oclyke-dev/RainbowForest/process_documentation/IMG_0713.JPG

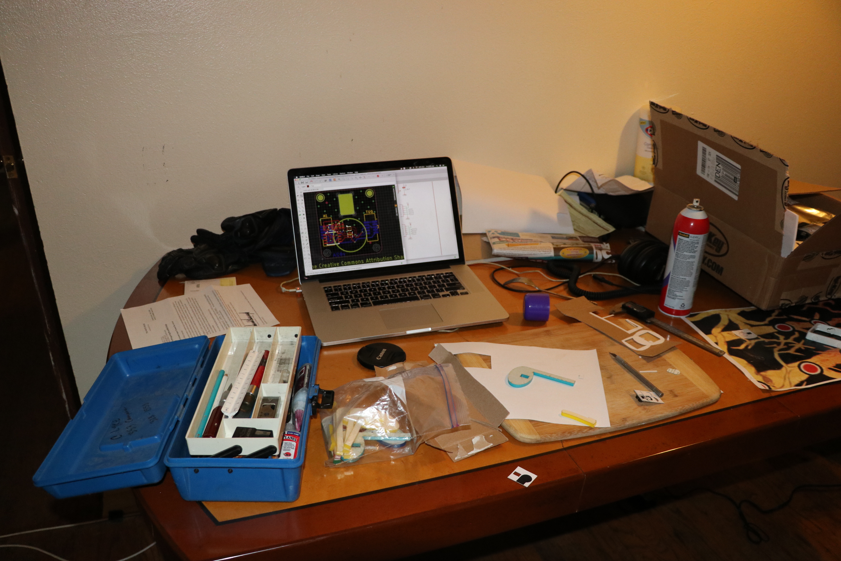
process_documentation/IMG_0713.JPG
