oclyke-dev/RainbowForest/process_documentation/IMG_0714.JPG

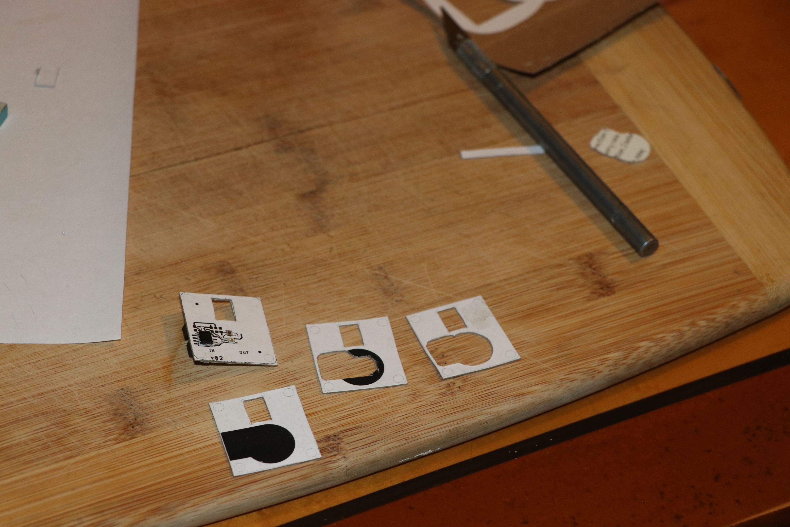
process_documentation/IMG_0714.JPG
