oclyke-dev/RainbowForest/process_documentation/IMG_0716.JPG

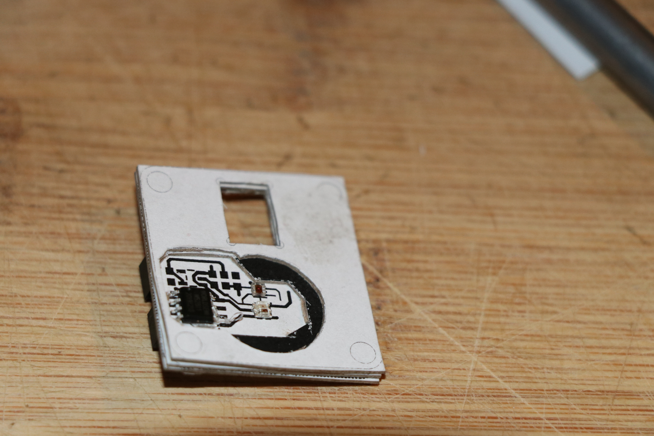
process_documentation/IMG_0716.JPG
