oclyke-dev/RainbowForest/process_documentation/IMG_0717.JPG

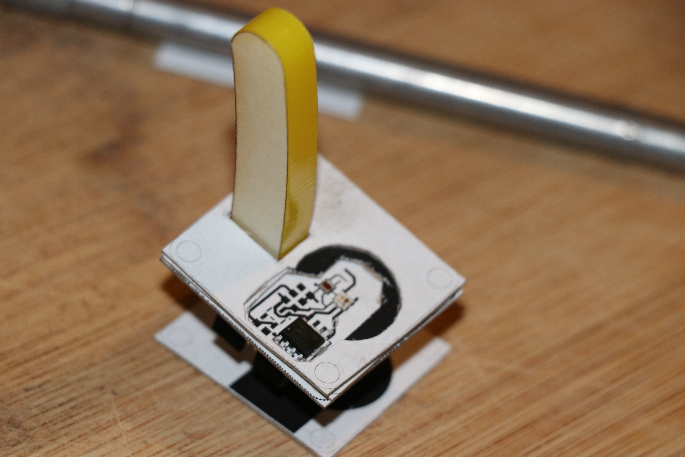
process_documentation/IMG_0717.JPG
