oclyke-dev/RainbowForest/process_documentation/IMG_0719.JPG

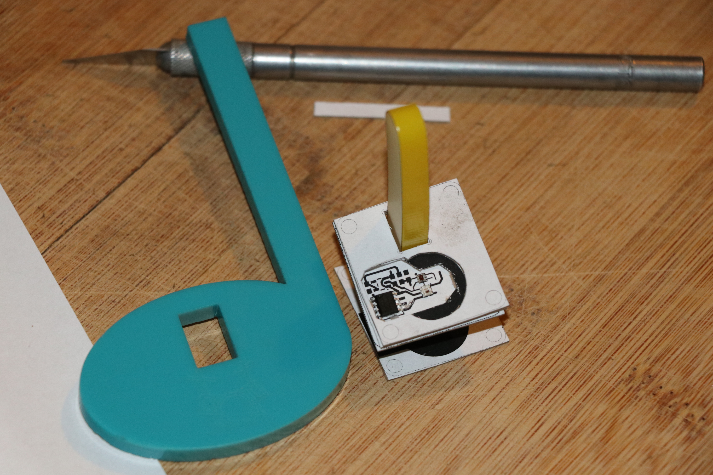
process_documentation/IMG_0719.JPG
