oclyke-dev/RainbowForest/process_documentation/IMG_0720.JPG

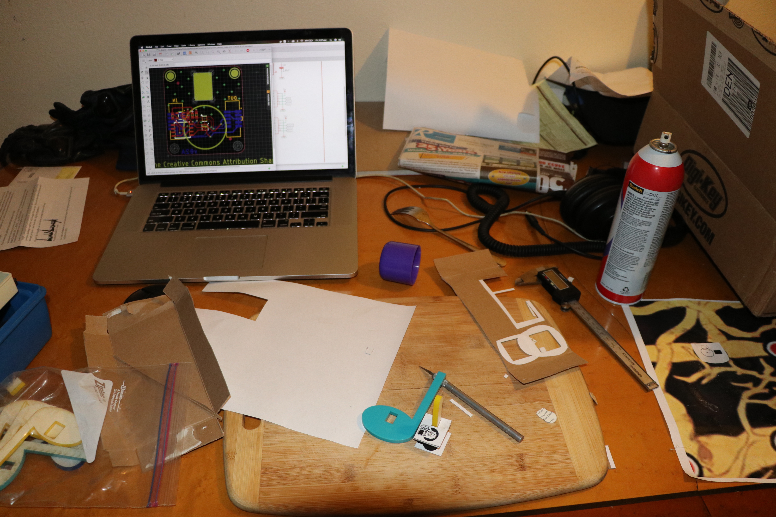
process_documentation/IMG_0720.JPG
