oclyke-dev/RainbowForest/process_documentation/Screen Shot 2020-04-22 at 2.14.59 PM.png

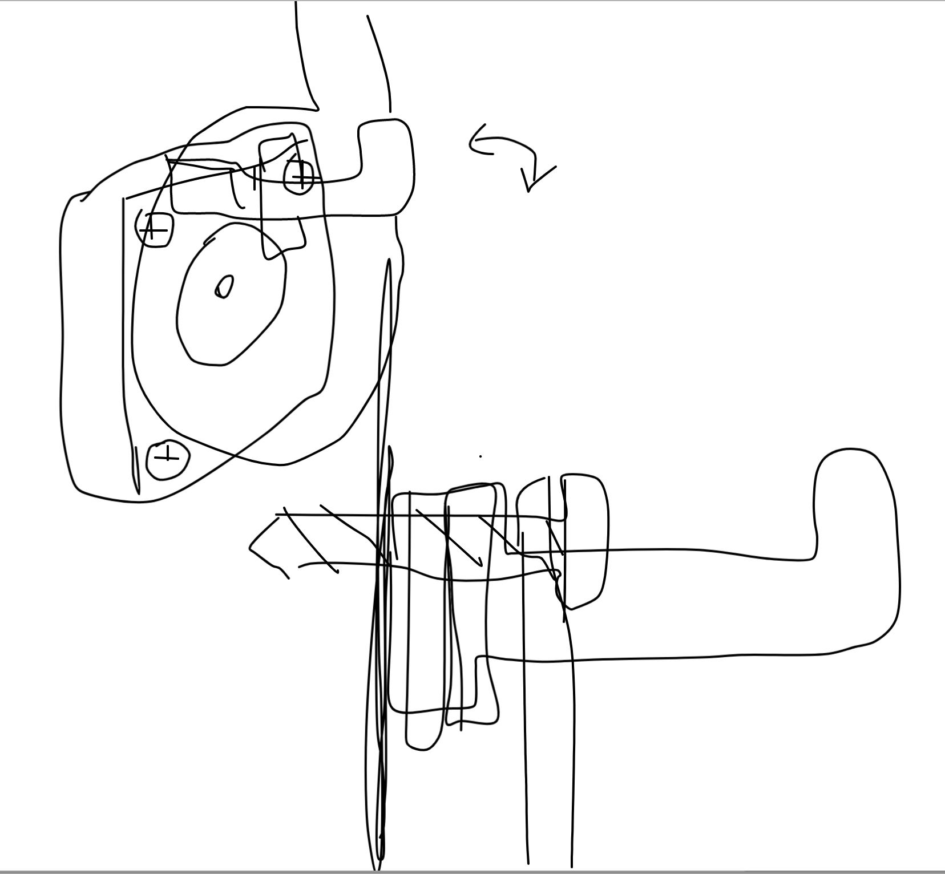
process_documentation/Screen Shot 2020-04-22 at 2.14.59 PM.png
