oclyke-dev/RainbowForest/firmware/components/isl29125/isl29125.cpp

/******************************************************************************
SparkFunISL29125.cpp
Core implementation file for the ISL29125 RGB sensor library.
Jordan McConnell @ SparkFun Electronics
25 Mar 2014
https://github.com/sparkfun/ISL29125_Breakout

This file implements the functions of the SFE_ISL29125 sensor class as well as
providing documentation on what each function does.

Developed/Tested with:
Arduino Uno
Arduino IDE 1.0.5

This code is beerware; if you see me (or any other SparkFun employee) at the local, and you've found our code helpful, please buy us a round!
Distributed as-is; no warranty is given.
******************************************************************************/

#include "isl29125.h"

// Constructor - Creates sensor object and sets I2C address
SFE_ISL29125::SFE_ISL29125(TwoWire* i2c, uint8_t addr)
{
  _i2c = i2c;
  _addr = addr;
}

// Destructor - Deletes sensor object
SFE_ISL29125::~SFE_ISL29125()
{

}

// Initialize - returns true if successful
// Starts Wire/I2C Communication
// Verifies sensor is there by checking its device ID
// Resets all registers/configurations to factory default
// Sets configuration registers for the common use case
bool SFE_ISL29125::init()
{
  bool ret = true;
  uint8_t data = 0x00;

  // // Start I2C
  // _i2c->begin(); // allow users to begin the sensor i2c port manually (b/c wire.begin re-assigns the pin functions)

  // Check device ID
  data = read8(DEVICE_ID);
  if (data != 0x7D)
  {
    ret &= false;
  }

  // Reset registers
  ret &= reset();

  // Set to RGB mode, 10k lux, and high IR compensation
  ret &= config(CFG1_MODE_RGB | CFG1_10KLUX, CFG2_IR_ADJUST_HIGH, CFG_DEFAULT);

  return ret;
}

// Reset all registers - returns true if successful
bool SFE_ISL29125::reset()
{
  uint8_t data = 0x00;
  // Reset registers
  write8(DEVICE_ID, 0x46);
  // Check reset
  data = read8(CONFIG_1);
  data |= read8(CONFIG_2);
  data |= read8(CONFIG_3);
  data |= read8(STATUS);
  if (data != 0x00)
  {
    return false;
  }
  return true;
}

// Setup Configuration registers (three registers) - returns true if successful
// Use CONFIG1 variables from SFE_ISL29125.h for first parameter config1, CONFIG2 for config2, 3 for 3
// Use CFG_DEFAULT for default configuration for that register
bool SFE_ISL29125::config(uint8_t config1, uint8_t config2, uint8_t config3)
{
  bool ret = true;
  uint8_t data = 0x00;

  // Set 1st configuration register
  write8(CONFIG_1, config1);
  // Set 2nd configuration register
  write8(CONFIG_2, config2);
  // Set 3rd configuration register
  write8(CONFIG_3, config3);

  // Check if configurations were set correctly
  data = read8(CONFIG_1);
  if (data != config1)
  {
    ret &= false;
  }
  data = read8(CONFIG_2);
  if (data != config2)
  {
    ret &= false;
  }
  data = read8(CONFIG_3);
  if (data != config3)
  {
    ret &= false;
  }
  return ret;
}

// Sets upper threshold value for triggering interrupts
void SFE_ISL29125::setUpperThreshold(uint16_t data)
{
  write16(THRESHOLD_HL, data);
}

// Sets lower threshold value for triggering interrupts
void SFE_ISL29125::setLowerThreshold(uint16_t data)
{
  write16(THRESHOLD_LL, data);
}

// Check what the upper threshold is, 0xFFFF by default
uint16_t SFE_ISL29125::readUpperThreshold()
{
  return read16(THRESHOLD_HL);
}

// Check what the upper threshold is, 0x0000 by default
uint16_t SFE_ISL29125::readLowerThreshold()
{
  return read16(THRESHOLD_LL);
}

// Read the latest Sensor ADC reading for the color Red
uint16_t SFE_ISL29125::readRed()
{
  return read16(RED_L);
}

// Read the latest Sensor ADC reading for the color Green
uint16_t SFE_ISL29125::readGreen()
{
  return read16(GREEN_L);
}

// Read the latest Sensor ADC reading for the color Blue
uint16_t SFE_ISL29125::readBlue()
{
  return read16(BLUE_L);
}

// Check status flag register that allows for checking for interrupts, brownouts, and ADC conversion completions
uint8_t SFE_ISL29125::readStatus()
{
  return read8(STATUS);
}

// Generic I2C read register (single byte)
uint8_t SFE_ISL29125::read8(uint8_t reg)
{
  _i2c->beginTransmission(_addr);
  _i2c->write(reg);
  _i2c->endTransmission();
//  _i2c->beginTransmission(_addr);
  _i2c->requestFrom(_addr,(uint8_t)1);
  uint8_t data = _i2c->read();
//  _i2c->endTransmission();

  return data;
}

// Generic I2C write data to register (single byte)
void SFE_ISL29125::write8(uint8_t reg, uint8_t data)
{
  _i2c->beginTransmission(_addr);
  _i2c->write(reg);
  _i2c->write(data);
  _i2c->endTransmission();

  return;
}

// Generic I2C read registers (two bytes, LSB first)
uint16_t SFE_ISL29125::read16(uint8_t reg)
{
  uint16_t data = 0x0000;

  _i2c->beginTransmission(_addr);
  _i2c->write(reg);
  _i2c->endTransmission();

//  _i2c->beginTransmission(_addr);
  _i2c->requestFrom(_addr, (uint8_t)2); // request 2 bytes of data
  data = _i2c->read();
  data |= (_i2c->read() << 8);
//  _i2c->endTransmission();

  return data;
}

// Generic I2C write data to registers (two bytes, LSB first)
void SFE_ISL29125::write16(uint8_t reg, uint16_t data)
{
  _i2c->beginTransmission(_addr);
  _i2c->write(reg);
  _i2c->write(data);
  _i2c->write(data>>8);
  _i2c->endTransmission();
}
